CasaJasmina/OSCOLA/code/ConfigureYourYun/yunWIFIConfig/password.h

const String yunName="arduino";
const String yunPsw="arduino";
const String wifissid="your wifi ssid";
const String wifipsw="your wifi psw";
const String wifiAPname="my_Arduino_Yun"; //this is the name of the access point you want the yun to create if somethings goes wrong with the connection to the wifi
